thehall16/ats-capstone/mcp16331_buck.kicad_sch

## KiCad design mcp16331_buck.kicad_sch (2025-11-17)

Schematic: mcp16331_buck.kicad_sch

Parts:
C1: 47uF 25V
C2, C3: 22uF 6.3V X7R
C4: 10pF
D1: SS14 Schottky
F1: 0.75A Polyfuse
J1: Barrel Jack 5.5x2.1mm
L1: 33uH Shielded
R1: 316k
R2: 100k
U1: MCP16331
