thehall16/ats-capstone/test.kicad_sch

## KiCad design test.kicad_sch (2025-11-17)

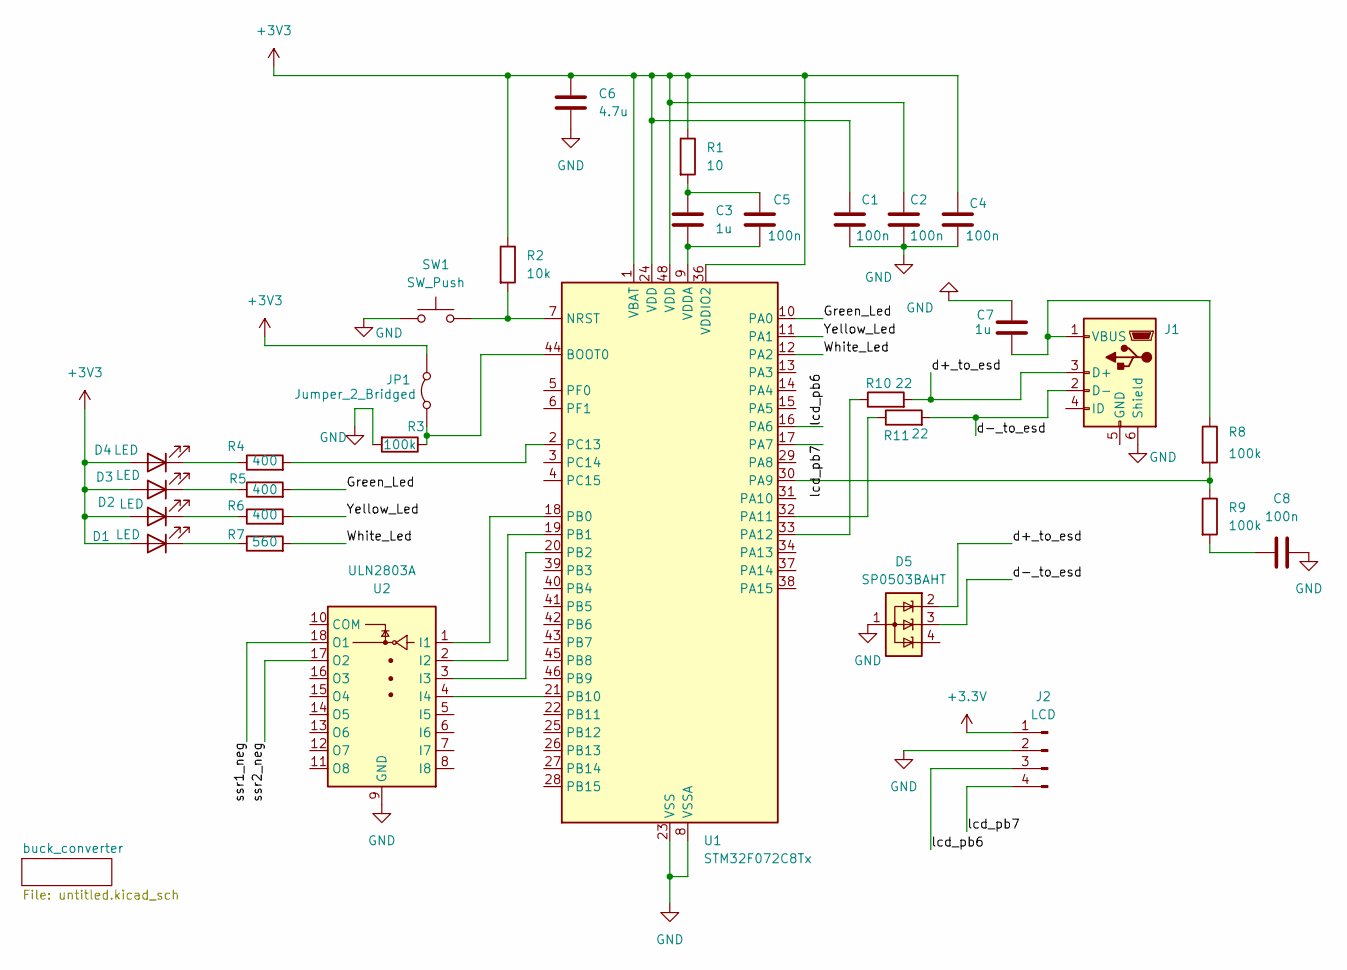
[picture p3: schematic test.kicad_sch]

Parts:
C1: 100n; USB_Micro-B_Molex-105017-0001
C2, C4, C5, C8: 100n
C3, C7: 1u
C6: 4.7u
D1, D2, D3, D4: LED
D5: SP0503BAHT; SOT-143
J1: USB_B_Micro
J2: LCD
JP1: Jumper_2_Bridged
R1: 10
R2: 10k
R3, R8, R9: 100k
R4, R5, R6: 400
R7: 560
R10, R11: 22
SW1: SW_Push
U1: STM32F072C8Tx; LQFP-48_7x7mm_P0.5mm
U2: ULN2803A

Connections:
+3.3V: J2.1
+3V3: C1.1, C2.1, C4.1, C6.1, D1.2 (A), D2.2 (A), D3.2 (A), D4.2 (A), JP1.2 (B), R1.1, R2.1, U1.1 (VBAT), U1.24 (VDD), U1.36 (VDDIO2), U1.48 (VDD)
GND: C1.2, C2.2, C4.2, C6.2, C7.1, C8.2, D5.1 (A), J1.6 (Shield), J2.2, R3.2, SW1.1, U1.8 (VSSA), U1.23 (VSS), U1.35 (VSS), U1.47 (VSS), U2.9 (GND)
Green_Led: R5.2, U1.10 (PA0)
unnamed: C3.1, C5.1, R1.2
unnamed: C3.2, C5.2, U1.9 (VDDA)
unnamed: C7.2, J1.1 (VBUS), R8.1
unnamed: C8.1, R9.2
unnamed: D1.1 (K), R7.1
unnamed: D2.1 (K), R6.1
unnamed: D3.1 (K), R5.1
unnamed: D4.1 (K), R4.1
unnamed: JP1.1 (A), R3.1, U1.44 (BOOT0)
unnamed: R2.2, SW1.2, U1.7 (NRST)
unnamed: R4.2, U1.2 (PC13)
unnamed: R8.2, R9.1, U1.30 (PA9)
unnamed: R10.1, U1.33 (PA12)
unnamed: R11.1, U1.32 (PA11)
unnamed: U1.18 (PB0), U2.1 (I1)
unnamed: U1.19 (PB1), U2.2 (I2)
unnamed: U1.20 (PB2), U2.3 (I3)
unnamed: U1.21 (PB10), U2.4 (I4)
White_Led: R7.2, U1.12 (PA2)
Yellow_Led: R6.2, U1.11 (PA1)
d+_to_esd: D5.2 (K), J1.3 (D+), R10.2
d-_to_esd: D5.3 (K), J1.2 (D-), R11.2
lcd_pb6: J2.3, U1.16 (PA6)
lcd_pb7: J2.4, U1.17 (PA7)
ssr1_neg: U2.18 (O1)
ssr2_neg: U2.17 (O2)
