thehall16/ats-capstone/untitled.kicad_sch

## KiCad design untitled.kicad_sch (2025-11-17)

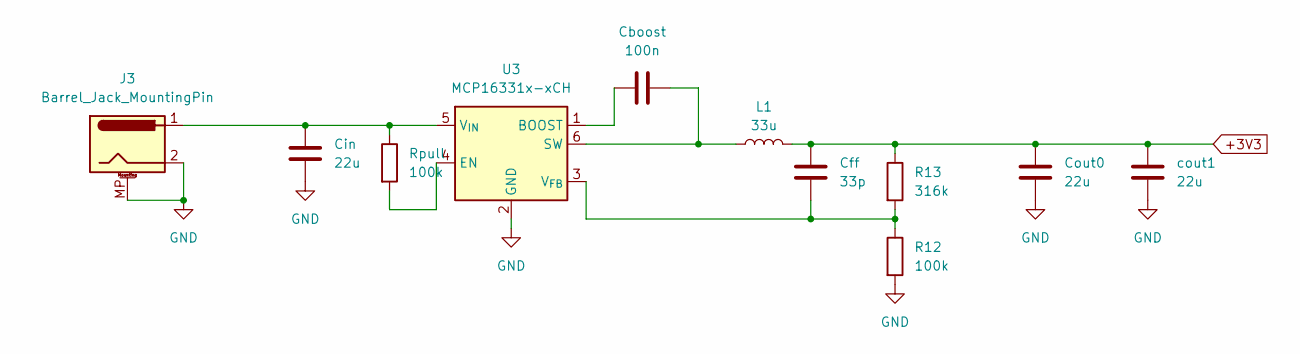
[picture p4: schematic untitled.kicad_sch]

Parts:
Cboost: 100n
Cff: 33p
Cin: 22u
Cout0: 22u
J3: Barrel_Jack_MountingPin
L1: 33u
R12: 100k
R13: 316k
Rpull: 100k
U3: MCP16331x-xCH; SOT-23-6
cout1: 22u

Connections:
+3V3: Cff.1, Cout0.1, L1.2, R13.1, cout1.1
GND: Cin.2, Cout0.2, J3.2, J3.MP (MountPin), R12.2, U3.2 (GND), cout1.2
unnamed: Cboost.1, L1.1, U3.6 (SW)
unnamed: Cboost.2, U3.1 (BOOST)
unnamed: Cff.2, R12.1, R13.2, U3.3 (V_{FB})
unnamed: Cin.1, J3.1, Rpull.1, U3.5 (V_{IN})
unnamed: Rpull.2, U3.4 (EN)
