thehall16/ats-capstone/generator.h

#ifndef GENERATOR_H
#define GENERATOR_H

//#include "main.h"

// Functions to control generator
void generator_startup_sequence(void); // Full startup sequence
void generator_stop(void);             // Stop generator immediately

#endif
